TheRealKasumi/NikoLight/mcu/src/led/driver/Pixel.cpp

/**
 * @file Pixel.cpp
 * @author TheRealKasumi
 * @brief Implementation of the {@link NL::Pixel} class.
 *
 * @copyright Copyright (c) 2023 TheRealKasumi
 *
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
 */
#include "led/driver/Pixel.h"

/**
 * @brief Create a new instance of {@link NL::Pixel}.
 */
NL::Pixel::Pixel()
{
	this->setColor(NL::Pixel::ColorCode::Black);
}

/**
 * @brief Create a new instance of {@link NL::Pixel}.
 * @param colorCode 24 bit color code
 */
NL::Pixel::Pixel(const uint32_t colorCode)
{
	this->setColor(colorCode);
}

/**
 * @brief Create a new instance of {@link NL::Pixel}.
 * @param colorCode one of the html color codes
 */
NL::Pixel::Pixel(const NL::Pixel::ColorCode colorCode)
{
	this->setColor(colorCode);
}

/**
 * @brief Create a new instance of {@link NL::Pixel}.
 * @param red red value
 * @param green green value
 * @param blue blue value
 */
NL::Pixel::Pixel(const uint8_t red, const uint8_t green, const uint8_t blue)
{
	this->setColor(red, green, blue);
}

/***
 * Destroy the {@link NL::Pixel} isntance.
 */
NL::Pixel::~Pixel()
{
}

/**
 * @brief Set the pixel color.
 * @param colorCode 24 bit color code
 */
void NL::Pixel::setColor(const uint32_t colorCode)
{
	this->red = (colorCode & 0xff0000) >> 16;
	this->green = (colorCode & 0x00ff00) >> 8;
	this->blue = (colorCode & 0x0000ff);
}

/**
 * @brief Set the pixel color.
 * @param colorCode one of the html color codes
 */
void NL::Pixel::setColor(const NL::Pixel::ColorCode colorCode)
{
	this->red = (static_cast<uint32_t>(colorCode) & 0xff0000) >> 16;
	this->green = (static_cast<uint32_t>(colorCode) & 0x00ff00) >> 8;
	this->blue = (static_cast<uint32_t>(colorCode) & 0x0000ff);
}

/**
 * @brief Set the pixel color.
 * @param red red value
 * @param green green value
 * @param blue blue value
 */
void NL::Pixel::setColor(const uint8_t red, const uint8_t green, const uint8_t blue)
{
	this->red = red;
	this->green = green;
	this->blue = blue;
}
