TheRealKasumi/NikoLight/mcu/src/server/ResetEndpoint.cpp

/**
 * @file ResetEndpoint.h
 * @author TheRealKasumi
 * @brief Contains a REST endpoint to remotely reset the controller in case something is going wrong.
 *
 * @copyright Copyright (c) 2023 TheRealKasumi
 *
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
 */
#include "server/ResetEndpoint.h"

FS *NL::ResetEndpoint::fileSystem = nullptr;

/**
 * @brief Add all request handler for this {@link NL::RestEndpoint} to the {@link NL::WebServerManager}.
 */
void NL::ResetEndpoint::begin(FS *_fileSystem)
{
	NL::ResetEndpoint::fileSystem = _fileSystem;
	NL::WebServerManager::addRequestHandler((getBaseUri() + F("reset/soft")).c_str(), http_method::HTTP_POST, NL::ResetEndpoint::handleSoftReset);
	NL::WebServerManager::addRequestHandler((getBaseUri() + F("reset/hard")).c_str(), http_method::HTTP_POST, NL::ResetEndpoint::handleHardReset);
}

/**
 * @brief Handler function for the soft reset.
 */
void NL::ResetEndpoint::handleSoftReset()
{
	NL::Logger::log(NL::Logger::LogLevel::INFO, SOURCE_LOCATION, F("Received request to execute a soft reset."));
	NL::ResetEndpoint::sendSimpleResponse(200, F("I will reboot for you in 3 seconds."));
	NL::Updater::reboot(F("Soft Reset"), 3000);
}

/**
 * @brief Handler function for the hard reset. This also deletes the configuration to start with defaults.
 */
void NL::ResetEndpoint::handleHardReset()
{
	NL::Logger::log(NL::Logger::LogLevel::INFO, SOURCE_LOCATION, F("Received request to execute a hard reset."));
	NL::ResetEndpoint::sendSimpleResponse(200, F("I will reset my configuration and then reboot for you in 3 seconds."));

	if (!NL::ResetEndpoint::fileSystem->remove(CONFIGURATION_FILE_NAME))
	{
		NL::Logger::log(NL::Logger::LogLevel::WARN, SOURCE_LOCATION, F("Failed to remove configuration. This might be normal if it was not saved before."));
	}
	else
	{
		NL::Logger::log(NL::Logger::LogLevel::INFO, SOURCE_LOCATION, F("Configuration was reset."));
	}

	NL::Updater::reboot(F("Hard Reset"), 3000);
}
