TheRealKasumi/NikoLight/ui/pnpm-lock.yaml

lockfileVersion: '6.1'

settings:
  autoInstallPeers: true
  excludeLinksFromLockfile: false

dependencies:
  '@heroicons/react':
    specifier: ^2.0.16
    version: 2.0.16(react@18.2.0)
  '@radix-ui/react-alert-dialog':
    specifier: ^1.0.3
    version: 1.0.3(@types/react@18.0.28)(react-dom@18.2.0)(react@18.2.0)
  '@radix-ui/react-collapsible':
    specifier: ^1.0.2
    version: 1.0.2(react-dom@18.2.0)(react@18.2.0)
  '@radix-ui/react-select':
    specifier: ^1.2.1
    version: 1.2.1(@types/react@18.0.28)(react-dom@18.2.0)(react@18.2.0)
  '@radix-ui/react-slider':
    specifier: ^1.1.1
    version: 1.1.1(react-dom@18.2.0)(react@18.2.0)
  '@radix-ui/react-switch':
    specifier: ^1.0.2
    version: 1.0.2(react-dom@18.2.0)(react@18.2.0)
  '@radix-ui/react-toast':
    specifier: ^1.1.3
    version: 1.1.3(react-dom@18.2.0)(react@18.2.0)
  '@radix-ui/react-toggle-group':
    specifier: ^1.0.3
    version: 1.0.3(react-dom@18.2.0)(react@18.2.0)
  '@tanstack/react-query':
    specifier: ^4.27.0
    version: 4.27.0(react-dom@18.2.0)(react@18.2.0)
  '@tanstack/react-router':
    specifier: 0.0.1-beta.83
    version: 0.0.1-beta.83(react-dom@18.2.0)(react@18.2.0)
  file-saver:
    specifier: ^2.0.5
    version: 2.0.5
  hex-rgb:
    specifier: ^5.0.0
    version: 5.0.0
  i18next:
    specifier: ^22.4.12
    version: 22.4.12
  i18next-browser-languagedetector:
    specifier: ^7.0.1
    version: 7.0.1
  i18next-http-backend:
    specifier: ^2.2.0
    version: 2.2.0
  ky:
    specifier: ^0.33.3
    version: 0.33.3
  react:
    specifier: ^18.2.0
    version: 18.2.0
  react-dom:
    specifier: ^18.2.0
    version: 18.2.0(react@18.2.0)
  react-error-boundary:
    specifier: ^3.1.4
    version: 3.1.4(react@18.2.0)
  react-hook-form:
    specifier: ^7.43.7
    version: 7.43.7(react@18.2.0)
  react-i18next:
    specifier: ^12.2.0
    version: 12.2.0(i18next@22.4.12)(react-dom@18.2.0)(react@18.2.0)
  rgb-hex:
    specifier: ^4.0.1
    version: 4.0.1
  swagger-ui-react:
    specifier: ^4.18.1
    version: 4.18.1(@types/react-dom@18.0.11)(@types/react@18.0.28)(react-dom@18.2.0)(react@18.2.0)

devDependencies:
  '@tanstack/eslint-plugin-query':
    specifier: ^4.27.0
    version: 4.27.0
  '@tanstack/react-query-devtools':
    specifier: ^4.27.0
    version: 4.27.0(@tanstack/react-query@4.27.0)(react-dom@18.2.0)(react@18.2.0)
  '@tanstack/react-router-devtools':
    specifier: 0.0.1-beta.83
    version: 0.0.1-beta.83(react-dom@18.2.0)(react@18.2.0)
  '@types/file-saver':
    specifier: ^2.0.5
    version: 2.0.5
  '@types/prettier':
    specifier: ^2.7.2
    version: 2.7.2
  '@types/react':
    specifier: ^18.0.28
    version: 18.0.28
  '@types/react-dom':
    specifier: ^18.0.11
    version: 18.0.11
  '@types/swagger-ui-react':
    specifier: ^4.11.0
    version: 4.11.0
  '@typescript-eslint/eslint-plugin':
    specifier: ^5.55.0
    version: 5.55.0(@typescript-eslint/parser@5.55.0)(eslint@8.36.0)(typescript@5.0.2)
  '@typescript-eslint/parser':
    specifier: ^5.55.0
    version: 5.55.0(eslint@8.36.0)(typescript@5.0.2)
  '@vitejs/plugin-react':
    specifier: ^3.1.0
    version: 3.1.0(vite@4.2.0)
  autoprefixer:
    specifier: ^10.4.14
    version: 10.4.14(postcss@8.4.21)
  classnames:
    specifier: ^2.3.2
    version: 2.3.2
  cssnano:
    specifier: ^5.1.15
    version: 5.1.15(postcss@8.4.21)
  eslint:
    specifier: ^8.36.0
    version: 8.36.0
  eslint-config-prettier:
    specifier: ^8.7.0
    version: 8.7.0(eslint@8.36.0)
  eslint-plugin-prettier:
    specifier: ^4.2.1
    version: 4.2.1(eslint-config-prettier@8.7.0)(eslint@8.36.0)(prettier@2.8.4)
  eslint-plugin-react:
    specifier: ^7.32.2
    version: 7.32.2(eslint@8.36.0)
  eslint-plugin-react-hooks:
    specifier: ^4.6.0
    version: 4.6.0(eslint@8.36.0)
  msw:
    specifier: ^1.1.0
    version: 1.1.0(typescript@5.0.2)
  postcss:
    specifier: ^8.4.21
    version: 8.4.21
  prettier:
    specifier: ^2.8.4
    version: 2.8.4
  prettier-plugin-tailwindcss:
    specifier: ^0.2.5
    version: 0.2.5(prettier@2.8.4)
  tailwind-merge:
    specifier: ^1.10.0
    version: 1.10.0
  tailwindcss:
    specifier: ^3.2.7
    version: 3.2.7(postcss@8.4.21)
  tailwindcss-radix:
    specifier: ^2.8.0
    version: 2.8.0
  typescript:
    specifier: ^5.0.2
    version: 5.0.2
  vite:
    specifier: ^4.2.0
    version: 4.2.0
  vite-plugin-svgr:
    specifier: ^2.4.0
    version: 2.4.0(vite@4.2.0)

packages:

  /@ampproject/remapping@2.2.0:
    resolution: {integrity: sha512-qRmjj8nj9qmLTQXXmaR1cck3UXSRMPrbsLJAasZpF+t3riI71BXed5ebIOYwQntykeZuhjsdweEc9BxH5Jc26w==}
    engines: {node: '>=6.0.0'}
    dependencies:
      '@jridgewell/gen-mapping': 0.1.1
      '@jridgewell/trace-mapping': 0.3.17
    dev: true

  /@babel/code-frame@7.18.6:
    resolution: {integrity: sha512-TDCmlK5eOvH+eH7cdAFlNXeVJqWIQ7gW9tY1GJIpUtFb6CmjVyq2VM3u71bOyR8CRihcCgMUYoDNyLXao3+70Q==}
    engines: {node: '>=6.9.0'}
    dependencies:
      '@babel/highlight': 7.18.6
    dev: true

  /@babel/compat-data@7.20.0:
    resolution: {integrity: sha512-Gt9jszFJYq7qzXVK4slhc6NzJXnOVmRECWcVjF/T23rNXD9NtWQ0W3qxdg+p9wWIB+VQw3GYV/U2Ha9bRTfs4w==}
    engines: {node: '>=6.9.0'}
    dev: true

  /@babel/compat-data@7.20.10:
    resolution: {integrity: sha512-sEnuDPpOJR/fcafHMjpcpGN5M2jbUGUHwmuWKM/YdPzeEDJg8bgmbcWQFUfE32MQjti1koACvoPVsDe8Uq+idg==}
    engines: {node: '>=6.9.0'}
    dev: true

  /@babel/core@7.20.12:
    resolution: {integrity: sha512-XsMfHovsUYHFMdrIHkZphTN/2Hzzi78R08NuHfDBehym2VsPDL6Zn/JAD/JQdnRvbSsbQc4mVaU1m6JgtTEElg==}
    engines: {node: '>=6.9.0'}
    dependencies:
      '@ampproject/remapping': 2.2.0
      '@babel/code-frame': 7.18.6
      '@babel/generator': 7.20.7
      '@babel/helper-compilation-targets': 7.20.7(@babel/core@7.20.12)
      '@babel/helper-module-transforms': 7.20.11
      '@babel/helpers': 7.20.7
      '@babel/parser': 7.20.7
      '@babel/template': 7.20.7
      '@babel/traverse': 7.20.12
      '@babel/types': 7.20.7
      convert-source-map: 1.9.0
      debug: 4.3.4
      gensync: 1.0.0-beta.2
      json5: 2.2.3
      semver: 6.3.0
    transitivePeerDependencies:
      - supports-color
    dev: true

  /@babel/core@7.20.5:
    resolution: {integrity: sha512-UdOWmk4pNWTm/4DlPUl/Pt4Gz4rcEMb7CY0Y3eJl5Yz1vI8ZJGmHWaVE55LoxRjdpx0z259GE9U5STA9atUinQ==}
    engines: {node: '>=6.9.0'}
    dependencies:
      '@ampproject/remapping': 2.2.0
      '@babel/code-frame': 7.18.6
      '@babel/generator': 7.20.5
      '@babel/helper-compilation-targets': 7.20.0(@babel/core@7.20.5)
      '@babel/helper-module-transforms': 7.20.2
      '@babel/helpers': 7.20.6
      '@babel/parser': 7.20.5
      '@babel/template': 7.18.10
      '@babel/traverse': 7.20.5
      '@babel/types': 7.20.5
      convert-source-map: 1.9.0
      debug: 4.3.4
      gensync: 1.0.0-beta.2
      json5: 2.2.1
      semver: 6.3.0
    transitivePeerDependencies:
      - supports-color
    dev: true

  /@babel/generator@7.20.5:
    resolution: {integrity: sha512-jl7JY2Ykn9S0yj4DQP82sYvPU+T3g0HFcWTqDLqiuA9tGRNIj9VfbtXGAYTTkyNEnQk1jkMGOdYka8aG/lulCA==}
    engines: {node: '>=6.9.0'}
    dependencies:
      '@babel/types': 7.20.5
      '@jridgewell/gen-mapping': 0.3.2
      jsesc: 2.5.2
    dev: true

  /@babel/generator@7.20.7:
    resolution: {integrity: sha512-7wqMOJq8doJMZmP4ApXTzLxSr7+oO2jroJURrVEp6XShrQUObV8Tq/D0NCcoYg2uHqUrjzO0zwBjoYzelxK+sw==}
    engines: {node: '>=6.9.0'}
    dependencies:
      '@babel/types': 7.20.7
      '@jridgewell/gen-mapping': 0.3.2
      jsesc: 2.5.2
    dev: true

  /@babel/helper-compilation-targets@7.20.0(@babel/core@7.20.5):
    resolution: {integrity: sha512-0jp//vDGp9e8hZzBc6N/KwA5ZK3Wsm/pfm4CrY7vzegkVxc65SgSn6wYOnwHe9Js9HRQ1YTCKLGPzDtaS3RoLQ==}
    engines: {node: '>=6.9.0'}
    peerDependencies:
      '@babel/core': ^7.0.0
    dependencies:
      '@babel/compat-data': 7.20.0
      '@babel/core': 7.20.5
      '@babel/helper-validator-option': 7.18.6
      browserslist: 4.21.5
      semver: 6.3.0
    dev: true

  /@babel/helper-compilation-targets@7.20.7(@babel/core@7.20.12):
    resolution: {integrity: sha512-4tGORmfQcrc+bvrjb5y3dG9Mx1IOZjsHqQVUz7XCNHO+iTmqxWnVg3KRygjGmpRLJGdQSKuvFinbIb0CnZwHAQ==}
    engines: {node: '>=6.9.0'}
    peerDependencies:
      '@babel/core': ^7.0.0
    dependencies:
      '@babel/compat-data': 7.20.10
      '@babel/core': 7.20.12
      '@babel/helper-validator-option': 7.18.6
      browserslist: 4.21.5
      lru-cache: 5.1.1
      semver: 6.3.0
    dev: true

  /@babel/helper-environment-visitor@7.18.9:
    resolution: {integrity: sha512-3r/aACDJ3fhQ/EVgFy0hpj8oHyHpQc+LPtJoY9SzTThAsStm4Ptegq92vqKoE3vD706ZVFWITnMnxucw+S9Ipg==}
    engines: {node: '>=6.9.0'}
    dev: true

  /@babel/helper-function-name@7.19.0:
    resolution: {integrity: sha512-WAwHBINyrpqywkUH0nTnNgI5ina5TFn85HKS0pbPDfxFfhyR/aNQEn4hGi1P1JyT//I0t4OgXUlofzWILRvS5w==}
    engines: {node: '>=6.9.0'}
    dependencies:
      '@babel/template': 7.18.10
      '@babel/types': 7.20.5
    dev: true

  /@babel/helper-hoist-variables@7.18.6:
    resolution: {integrity: sha512-UlJQPkFqFULIcyW5sbzgbkxn2FKRgwWiRexcuaR8RNJRy8+LLveqPjwZV/bwrLZCN0eUHD/x8D0heK1ozuoo6Q==}
    engines: {node: '>=6.9.0'}
    dependencies:
      '@babel/types': 7.20.5
    dev: true

  /@babel/helper-module-imports@7.18.6:
    resolution: {integrity: sha512-0NFvs3VkuSYbFi1x2Vd6tKrywq+z/cLeYC/RJNFrIX/30Bf5aiGYbtvGXolEktzJH8o5E5KJ3tT+nkxuuZFVlA==}
    engines: {node: '>=6.9.0'}
    dependencies:
      '@babel/types': 7.20.5
    dev: true

  /@babel/helper-module-transforms@7.20.11:
    resolution: {integrity: sha512-uRy78kN4psmji1s2QtbtcCSaj/LILFDp0f/ymhpQH5QY3nljUZCaNWz9X1dEj/8MBdBEFECs7yRhKn8i7NjZgg==}
    engines: {node: '>=6.9.0'}
    dependencies:
      '@babel/helper-environment-visitor': 7.18.9
      '@babel/helper-module-imports': 7.18.6
      '@babel/helper-simple-access': 7.20.2
      '@babel/helper-split-export-declaration': 7.18.6
      '@babel/helper-validator-identifier': 7.19.1
      '@babel/template': 7.20.7
      '@babel/traverse': 7.20.12
      '@babel/types': 7.20.7
    transitivePeerDependencies:
      - supports-color
    dev: true

  /@babel/helper-module-transforms@7.20.2:
    resolution: {integrity: sha512-zvBKyJXRbmK07XhMuujYoJ48B5yvvmM6+wcpv6Ivj4Yg6qO7NOZOSnvZN9CRl1zz1Z4cKf8YejmCMh8clOoOeA==}
    engines: {node: '>=6.9.0'}
    dependencies:
      '@babel/helper-environment-visitor': 7.18.9
      '@babel/helper-module-imports': 7.18.6
      '@babel/helper-simple-access': 7.20.2
      '@babel/helper-split-export-declaration': 7.18.6
      '@babel/helper-validator-identifier': 7.19.1
      '@babel/template': 7.18.10
      '@babel/traverse': 7.20.5
      '@babel/types': 7.20.5
    transitivePeerDependencies:
      - supports-color
    dev: true

  /@babel/helper-plugin-utils@7.19.0:
    resolution: {integrity: sha512-40Ryx7I8mT+0gaNxm8JGTZFUITNqdLAgdg0hXzeVZxVD6nFsdhQvip6v8dqkRHzsz1VFpFAaOCHNn0vKBL7Czw==}
    engines: {node: '>=6.9.0'}
    dev: true

  /@babel/helper-simple-access@7.20.2:
    resolution: {integrity: sha512-+0woI/WPq59IrqDYbVGfshjT5Dmk/nnbdpcF8SnMhhXObpTq2KNBdLFRFrkVdbDOyUmHBCxzm5FHV1rACIkIbA==}
    engines: {node: '>=6.9.0'}
    dependencies:
      '@babel/types': 7.20.5
    dev: true

  /@babel/helper-split-export-declaration@7.18.6:
    resolution: {integrity: sha512-bde1etTx6ZyTmobl9LLMMQsaizFVZrquTEHOqKeQESMKo4PlObf+8+JA25ZsIpZhT/WEd39+vOdLXAFG/nELpA==}
    engines: {node: '>=6.9.0'}
    dependencies:
      '@babel/types': 7.20.5
    dev: true

  /@babel/helper-string-parser@7.19.4:
    resolution: {integrity: sha512-nHtDoQcuqFmwYNYPz3Rah5ph2p8PFeFCsZk9A/48dPc/rGocJ5J3hAAZ7pb76VWX3fZKu+uEr/FhH5jLx7umrw==}
    engines: {node: '>=6.9.0'}
    dev: true

  /@babel/helper-validator-identifier@7.19.1:
    resolution: {integrity: sha512-awrNfaMtnHUr653GgGEs++LlAvW6w+DcPrOliSMXWCKo597CwL5Acf/wWdNkf/tfEQE3mjkeD1YOVZOUV/od1w==}
    engines: {node: '>=6.9.0'}
    dev: true

  /@babel/helper-validator-option@7.18.6:
    resolution: {integrity: sha512-XO7gESt5ouv/LRJdrVjkShckw6STTaB7l9BrpBaAHDeF5YZT+01PCwmR0SJHnkW6i8OwW/EVWRShfi4j2x+KQw==}
    engines: {node: '>=6.9.0'}
    dev: true

  /@babel/helpers@7.20.6:
    resolution: {integrity: sha512-Pf/OjgfgFRW5bApskEz5pvidpim7tEDPlFtKcNRXWmfHGn9IEI2W2flqRQXTFb7gIPTyK++N6rVHuwKut4XK6w==}
    engines: {node: '>=6.9.0'}
    dependencies:
      '@babel/template': 7.18.10
      '@babel/traverse': 7.20.5
      '@babel/types': 7.20.5
    transitivePeerDependencies:
      - supports-color
    dev: true

  /@babel/helpers@7.20.7:
    resolution: {integrity: sha512-PBPjs5BppzsGaxHQCDKnZ6Gd9s6xl8bBCluz3vEInLGRJmnZan4F6BYCeqtyXqkk4W5IlPmjK4JlOuZkpJ3xZA==}
    engines: {node: '>=6.9.0'}
    dependencies:
      '@babel/template': 7.20.7
      '@babel/traverse': 7.20.12
      '@babel/types': 7.20.7
    transitivePeerDependencies:
      - supports-color
    dev: true

  /@babel/highlight@7.18.6:
    resolution: {integrity: sha512-u7stbOuYjaPezCuLj29hNW1v64M2Md2qupEKP1fHc7WdOA3DgLh37suiSrZYY7haUB7iBeQZ9P1uiRF359do3g==}
    engines: {node: '>=6.9.0'}
    dependencies:
      '@babel/helper-validator-identifier': 7.19.1
      chalk: 2.4.2
      js-tokens: 4.0.0
    dev: true

  /@babel/parser@7.20.5:
    resolution: {integrity: sha512-r27t/cy/m9uKLXQNWWebeCUHgnAZq0CpG1OwKRxzJMP1vpSU4bSIK2hq+/cp0bQxetkXx38n09rNu8jVkcK/zA==}
    engines: {node: '>=6.0.0'}
    hasBin: true
    dependencies:
      '@babel/types': 7.20.5
    dev: true

  /@babel/parser@7.20.7:
    resolution: {integrity: sha512-T3Z9oHybU+0vZlY9CiDSJQTD5ZapcW18ZctFMi0MOAl/4BjFF4ul7NVSARLdbGO5vDqy9eQiGTV0LtKfvCYvcg==}
    engines: {node: '>=6.0.0'}
    hasBin: true
    dependencies:
      '@babel/types': 7.20.7
    dev: true

  /@babel/plugin-transform-react-jsx-self@7.18.6(@babel/core@7.20.12):
    resolution: {integrity: sha512-A0LQGx4+4Jv7u/tWzoJF7alZwnBDQd6cGLh9P+Ttk4dpiL+J5p7NSNv/9tlEFFJDq3kjxOavWmbm6t0Gk+A3Ig==}
    engines: {node: '>=6.9.0'}
    peerDependencies:
      '@babel/core': ^7.0.0-0
    dependencies:
      '@babel/core': 7.20.12
      '@babel/helper-plugin-utils': 7.19.0
    dev: true

  /@babel/plugin-transform-react-jsx-source@7.19.6(@babel/core@7.20.12):
    resolution: {integrity: sha512-RpAi004QyMNisst/pvSanoRdJ4q+jMCWyk9zdw/CyLB9j8RXEahodR6l2GyttDRyEVWZtbN+TpLiHJ3t34LbsQ==}
    engines: {node: '>=6.9.0'}
    peerDependencies:
      '@babel/core': ^7.0.0-0
    dependencies:
      '@babel/core': 7.20.12
      '@babel/helper-plugin-utils': 7.19.0
    dev: true

  /@babel/runtime-corejs3@7.21.0:
    resolution: {integrity: sha512-TDD4UJzos3JJtM+tHX+w2Uc+KWj7GV+VKKFdMVd2Rx8sdA19hcc3P3AHFYd5LVOw+pYuSd5lICC3gm52B6Rwxw==}
    engines: {node: '>=6.9.0'}
    dependencies:
      core-js-pure: 3.26.1
      regenerator-runtime: 0.13.11
    dev: false

  /@babel/runtime@7.20.1:
    resolution: {integrity: sha512-mrzLkl6U9YLF8qpqI7TB82PESyEGjm/0Ly91jG575eVxMMlb8fYfOXFZIJ8XfLrJZQbm7dlKry2bJmXBUEkdFg==}
    engines: {node: '>=6.9.0'}
    dependencies:
      regenerator-runtime: 0.13.11
    dev: false

  /@babel/runtime@7.20.7:
    resolution: {integrity: sha512-UF0tvkUtxwAgZ5W/KrkHf0Rn0fdnLDU9ScxBrEVNUprE/MzirjK4MJUX1/BVDv00Sv8cljtukVK1aky++X1SjQ==}
    engines: {node: '>=6.9.0'}
    dependencies:
      regenerator-runtime: 0.13.11

  /@babel/template@7.18.10:
    resolution: {integrity: sha512-TI+rCtooWHr3QJ27kJxfjutghu44DLnasDMwpDqCXVTal9RLp3RSYNh4NdBrRP2cQAoG9A8juOQl6P6oZG4JxA==}
    engines: {node: '>=6.9.0'}
    dependencies:
      '@babel/code-frame': 7.18.6
      '@babel/parser': 7.20.5
      '@babel/types': 7.20.5
    dev: true

  /@babel/template@7.20.7:
    resolution: {integrity: sha512-8SegXApWe6VoNw0r9JHpSteLKTpTiLZ4rMlGIm9JQ18KiCtyQiAMEazujAHrUS5flrcqYZa75ukev3P6QmUwUw==}
    engines: {node: '>=6.9.0'}
    dependencies:
      '@babel/code-frame': 7.18.6
      '@babel/parser': 7.20.7
      '@babel/types': 7.20.7
    dev: true

  /@babel/traverse@7.20.12:
    resolution: {integrity: sha512-MsIbFN0u+raeja38qboyF8TIT7K0BFzz/Yd/77ta4MsUsmP2RAnidIlwq7d5HFQrH/OZJecGV6B71C4zAgpoSQ==}
    engines: {node: '>=6.9.0'}
    dependencies:
      '@babel/code-frame': 7.18.6
      '@babel/generator': 7.20.7
      '@babel/helper-environment-visitor': 7.18.9
      '@babel/helper-function-name': 7.19.0
      '@babel/helper-hoist-variables': 7.18.6
      '@babel/helper-split-export-declaration': 7.18.6
      '@babel/parser': 7.20.7
      '@babel/types': 7.20.7
      debug: 4.3.4
      globals: 11.12.0
    transitivePeerDependencies:
      - supports-color
    dev: true

  /@babel/traverse@7.20.5:
    resolution: {integrity: sha512-WM5ZNN3JITQIq9tFZaw1ojLU3WgWdtkxnhM1AegMS+PvHjkM5IXjmYEGY7yukz5XS4sJyEf2VzWjI8uAavhxBQ==}
    engines: {node: '>=6.9.0'}
    dependencies:
      '@babel/code-frame': 7.18.6
      '@babel/generator': 7.20.5
      '@babel/helper-environment-visitor': 7.18.9
      '@babel/helper-function-name': 7.19.0
      '@babel/helper-hoist-variables': 7.18.6
      '@babel/helper-split-export-declaration': 7.18.6
      '@babel/parser': 7.20.5
      '@babel/types': 7.20.5
      debug: 4.3.4
      globals: 11.12.0
    transitivePeerDependencies:
      - supports-color
    dev: true

  /@babel/types@7.20.5:
    resolution: {integrity: sha512-c9fst/h2/dcF7H+MJKZ2T0KjEQ8hY/BNnDk/H3XY8C4Aw/eWQXWn/lWntHF9ooUBnGmEvbfGrTgLWc+um0YDUg==}
    engines: {node: '>=6.9.0'}
    dependencies:
      '@babel/helper-string-parser': 7.19.4
      '@babel/helper-validator-identifier': 7.19.1
      to-fast-properties: 2.0.0
    dev: true

  /@babel/types@7.20.7:
    resolution: {integrity: sha512-69OnhBxSSgK0OzTJai4kyPDiKTIe3j+ctaHdIGVbRahTLAT7L3R9oeXHC2aVSuGYt3cVnoAMDmOCgJ2yaiLMvg==}
    engines: {node: '>=6.9.0'}
    dependencies:
      '@babel/helper-string-parser': 7.19.4
      '@babel/helper-validator-identifier': 7.19.1
      to-fast-properties: 2.0.0
    dev: true

  /@braintree/sanitize-url@6.0.2:
    resolution: {integrity: sha512-Tbsj02wXCbqGmzdnXNk0SOF19ChhRU70BsroIi4Pm6Ehp56in6vch94mfbdQ17DozxkL3BAVjbZ4Qc1a0HFRAg==}
    dev: false

  /@esbuild/android-arm64@0.17.12:
    resolution: {integrity: sha512-WQ9p5oiXXYJ33F2EkE3r0FRDFVpEdcDiwNX3u7Xaibxfx6vQE0Sb8ytrfQsA5WO6kDn6mDfKLh6KrPBjvkk7xA==}
    engines: {node: '>=12'}
    cpu: [arm64]
    os: [android]
    requiresBuild: true
    dev: true
    optional: true

  /@esbuild/android-arm@0.17.12:
    resolution: {integrity: sha512-E/sgkvwoIfj4aMAPL2e35VnUJspzVYl7+M1B2cqeubdBhADV4uPon0KCc8p2G+LqSJ6i8ocYPCqY3A4GGq0zkQ==}
    engines: {node: '>=12'}
    cpu: [arm]
    os: [android]
    requiresBuild: true
    dev: true
    optional: true

  /@esbuild/android-x64@0.17.12:
    resolution: {integrity: sha512-m4OsaCr5gT+se25rFPHKQXARMyAehHTQAz4XX1Vk3d27VtqiX0ALMBPoXZsGaB6JYryCLfgGwUslMqTfqeLU0w==}
    engines: {node: '>=12'}
    cpu: [x64]
    os: [android]
    requiresBuild: true
    dev: true
    optional: true

  /@esbuild/darwin-arm64@0.17.12:
    resolution: {integrity: sha512-O3GCZghRIx+RAN0NDPhyyhRgwa19MoKlzGonIb5hgTj78krqp9XZbYCvFr9N1eUxg0ZQEpiiZ4QvsOQwBpP+lg==}
    engines: {node: '>=12'}
    cpu: [arm64]
    os: [darwin]
    requiresBuild: true
    dev: true
    optional: true

  /@esbuild/darwin-x64@0.17.12:
    resolution: {integrity: sha512-5D48jM3tW27h1qjaD9UNRuN+4v0zvksqZSPZqeSWggfMlsVdAhH3pwSfQIFJwcs9QJ9BRibPS4ViZgs3d2wsCA==}
    engines: {node: '>=12'}
    cpu: [x64]
    os: [darwin]
    requiresBuild: true
    dev: true
    optional: true

  /@esbuild/freebsd-arm64@0.17.12:
    resolution: {integrity: sha512-OWvHzmLNTdF1erSvrfoEBGlN94IE6vCEaGEkEH29uo/VoONqPnoDFfShi41Ew+yKimx4vrmmAJEGNoyyP+OgOQ==}
    engines: {node: '>=12'}
    cpu: [arm64]
    os: [freebsd]
    requiresBuild: true
    dev: true
    optional: true

  /@esbuild/freebsd-x64@0.17.12:
    resolution: {integrity: sha512-A0Xg5CZv8MU9xh4a+7NUpi5VHBKh1RaGJKqjxe4KG87X+mTjDE6ZvlJqpWoeJxgfXHT7IMP9tDFu7IZ03OtJAw==}
    engines: {node: '>=12'}
    cpu: [x64]
    os: [freebsd]
    requiresBuild: true
    dev: true
    optional: true

  /@esbuild/linux-arm64@0.17.12:
    resolution: {integrity: sha512-cK3AjkEc+8v8YG02hYLQIQlOznW+v9N+OI9BAFuyqkfQFR+DnDLhEM5N8QRxAUz99cJTo1rLNXqRrvY15gbQUg==}
    engines: {node: '>=12'}
    cpu: [arm64]
    os: [linux]
    requiresBuild: true
    dev: true
    optional: true

  /@esbuild/linux-arm@0.17.12:
    resolution: {integrity: sha512-WsHyJ7b7vzHdJ1fv67Yf++2dz3D726oO3QCu8iNYik4fb5YuuReOI9OtA+n7Mk0xyQivNTPbl181s+5oZ38gyA==}
    engines: {node: '>=12'}
    cpu: [arm]
    os: [linux]
    requiresBuild: true
    dev: true
    optional: true

  /@esbuild/linux-ia32@0.17.12:
    resolution: {integrity: sha512-jdOBXJqcgHlah/nYHnj3Hrnl9l63RjtQ4vn9+bohjQPI2QafASB5MtHAoEv0JQHVb/xYQTFOeuHnNYE1zF7tYw==}
    engines: {node: '>=12'}
    cpu: [ia32]
    os: [linux]
    requiresBuild: true
    dev: true
    optional: true

  /@esbuild/linux-loong64@0.17.12:
    resolution: {integrity: sha512-GTOEtj8h9qPKXCyiBBnHconSCV9LwFyx/gv3Phw0pa25qPYjVuuGZ4Dk14bGCfGX3qKF0+ceeQvwmtI+aYBbVA==}
    engines: {node: '>=12'}
    cpu: [loong64]
    os: [linux]
    requiresBuild: true
    dev: true
    optional: true

  /@esbuild/linux-mips64el@0.17.12:
    resolution: {integrity: sha512-o8CIhfBwKcxmEENOH9RwmUejs5jFiNoDw7YgS0EJTF6kgPgcqLFjgoc5kDey5cMHRVCIWc6kK2ShUePOcc7RbA==}
    engines: {node: '>=12'}
    cpu: [mips64el]
    os: [linux]
    requiresBuild: true
    dev: true
    optional: true

  /@esbuild/linux-ppc64@0.17.12:
    resolution: {integrity: sha512-biMLH6NR/GR4z+ap0oJYb877LdBpGac8KfZoEnDiBKd7MD/xt8eaw1SFfYRUeMVx519kVkAOL2GExdFmYnZx3A==}
    engines: {node: '>=12'}
    cpu: [ppc64]
    os: [linux]
    requiresBuild: true
    dev: true
    optional: true

  /@esbuild/linux-riscv64@0.17.12:
    resolution: {integrity: sha512-jkphYUiO38wZGeWlfIBMB72auOllNA2sLfiZPGDtOBb1ELN8lmqBrlMiucgL8awBw1zBXN69PmZM6g4yTX84TA==}
    engines: {node: '>=12'}
    cpu: [riscv64]
    os: [linux]
    requiresBuild: true
    dev: true
    optional: true

  /@esbuild/linux-s390x@0.17.12:
    resolution: {integrity: sha512-j3ucLdeY9HBcvODhCY4b+Ds3hWGO8t+SAidtmWu/ukfLLG/oYDMaA+dnugTVAg5fnUOGNbIYL9TOjhWgQB8W5g==}
    engines: {node: '>=12'}
    cpu: [s390x]
    os: [linux]
    requiresBuild: true
    dev: true
    optional: true

  /@esbuild/linux-x64@0.17.12:
    resolution: {integrity: sha512-uo5JL3cgaEGotaqSaJdRfFNSCUJOIliKLnDGWaVCgIKkHxwhYMm95pfMbWZ9l7GeW9kDg0tSxcy9NYdEtjwwmA==}
    engines: {node: '>=12'}
    cpu: [x64]
    os: [linux]
    requiresBuild: true
    dev: true
    optional: true

  /@esbuild/netbsd-x64@0.17.12:
    resolution: {integrity: sha512-DNdoRg8JX+gGsbqt2gPgkgb00mqOgOO27KnrWZtdABl6yWTST30aibGJ6geBq3WM2TIeW6COs5AScnC7GwtGPg==}
    engines: {node: '>=12'}
    cpu: [x64]
    os: [netbsd]
    requiresBuild: true
    dev: true
    optional: true

  /@esbuild/openbsd-x64@0.17.12:
    resolution: {integrity: sha512-aVsENlr7B64w8I1lhHShND5o8cW6sB9n9MUtLumFlPhG3elhNWtE7M1TFpj3m7lT3sKQUMkGFjTQBrvDDO1YWA==}
    engines: {node: '>=12'}
    cpu: [x64]
    os: [openbsd]
    requiresBuild: true
    dev: true
    optional: true

  /@esbuild/sunos-x64@0.17.12:
    resolution: {integrity: sha512-qbHGVQdKSwi0JQJuZznS4SyY27tYXYF0mrgthbxXrZI3AHKuRvU+Eqbg/F0rmLDpW/jkIZBlCO1XfHUBMNJ1pg==}
    engines: {node: '>=12'}
    cpu: [x64]
    os: [sunos]
    requiresBuild: true
    dev: true
    optional: true

  /@esbuild/win32-arm64@0.17.12:
    resolution: {integrity: sha512-zsCp8Ql+96xXTVTmm6ffvoTSZSV2B/LzzkUXAY33F/76EajNw1m+jZ9zPfNJlJ3Rh4EzOszNDHsmG/fZOhtqDg==}
    engines: {node: '>=12'}
    cpu: [arm64]
    os: [win32]
    requiresBuild: true
    dev: true
    optional: true

  /@esbuild/win32-ia32@0.17.12:
    resolution: {integrity: sha512-FfrFjR4id7wcFYOdqbDfDET3tjxCozUgbqdkOABsSFzoZGFC92UK7mg4JKRc/B3NNEf1s2WHxJ7VfTdVDPN3ng==}
    engines: {node: '>=12'}
    cpu: [ia32]
    os: [win32]
    requiresBuild: true
    dev: true
    optional: true

  /@esbuild/win32-x64@0.17.12:
    resolution: {integrity: sha512-JOOxw49BVZx2/5tW3FqkdjSD/5gXYeVGPDcB0lvap0gLQshkh1Nyel1QazC+wNxus3xPlsYAgqU1BUmrmCvWtw==}
    engines: {node: '>=12'}
    cpu: [x64]
    os: [win32]
    requiresBuild: true
    dev: true
    optional: true

  /@eslint-community/eslint-utils@4.3.0(eslint@8.36.0):
    resolution: {integrity: sha512-v3oplH6FYCULtFuCeqyuTd9D2WKO937Dxdq+GmHOLL72TTRriLxz2VLlNfkZRsvj6PKnOPAtuT6dwrs/pA5DvA==}
    engines: {node: ^12.22.0 || ^14.17.0 || >=16.0.0}
    peerDependencies:
      eslint: ^6.0.0 || ^7.0.0 || >=8.0.0
    dependencies:
      eslint: 8.36.0
      eslint-visitor-keys: 3.3.0
    dev: true

  /@eslint-community/regexpp@4.4.0:
    resolution: {integrity: sha512-A9983Q0LnDGdLPjxyXQ00sbV+K+O+ko2Dr+CZigbHWtX9pNfxlaBkMR8X1CztI73zuEyEBXTVjx7CE+/VSwDiQ==}
    engines: {node: ^12.0.0 || ^14.0.0 || >=16.0.0}
    dev: true

  /@eslint/eslintrc@2.0.1:
    resolution: {integrity: sha512-eFRmABvW2E5Ho6f5fHLqgena46rOj7r7OKHYfLElqcBfGFHHpjBhivyi5+jOEQuSpdc/1phIZJlbC2te+tZNIw==}
    engines: {node: ^12.22.0 || ^14.17.0 || >=16.0.0}
    dependencies:
      ajv: 6.12.6
      debug: 4.3.4
      espree: 9.5.0
      globals: 13.19.0
      ignore: 5.2.1
      import-fresh: 3.3.0
      js-yaml: 4.1.0
      minimatch: 3.1.2
      strip-json-comments: 3.1.1
    transitivePeerDependencies:
      - supports-color
    dev: true

  /@eslint/js@8.36.0:
    resolution: {integrity: sha512-lxJ9R5ygVm8ZWgYdUweoq5ownDlJ4upvoWmO4eLxBYHdMo+vZ/Rx0EN6MbKWDJOSUGrqJy2Gt+Dyv/VKml0fjg==}
    engines: {node: ^12.22.0 || ^14.17.0 || >=16.0.0}
    dev: true

  /@floating-ui/core@0.7.3:
    resolution: {integrity: sha512-buc8BXHmG9l82+OQXOFU3Kr2XQx9ys01U/Q9HMIrZ300iLc8HLMgh7dcCqgYzAzf4BkoQvDcXf5Y+CuEZ5JBYg==}
    dev: false

  /@floating-ui/dom@0.5.4:
    resolution: {integrity: sha512-419BMceRLq0RrmTSDxn8hf9R3VCJv2K9PUfugh5JyEFmdjzDo+e8U5EdR8nzKq8Yj1htzLm3b6eQEEam3/rrtg==}
    dependencies:
      '@floating-ui/core': 0.7.3
    dev: false

  /@floating-ui/react-dom@0.7.2(@types/react@18.0.28)(react-dom@18.2.0)(react@18.2.0):
    resolution: {integrity: sha512-1T0sJcpHgX/u4I1OzIEhlcrvkUN8ln39nz7fMoE/2HDHrPiMFoOGR7++GYyfUmIQHkkrTinaeQsO3XWubjSvGg==}
    peerDependencies:
      react: '>=16.8.0'
      react-dom: '>=16.8.0'
    dependencies:
      '@floating-ui/dom': 0.5.4
      react: 18.2.0
      react-dom: 18.2.0(react@18.2.0)
      use-isomorphic-layout-effect: 1.1.2(@types/react@18.0.28)(react@18.2.0)
    transitivePeerDependencies:
      - '@types/react'
    dev: false

  /@heroicons/react@2.0.16(react@18.2.0):
    resolution: {integrity: sha512-x89rFxH3SRdYaA+JCXwfe+RkE1SFTo9GcOkZettHer71Y3T7V+ogKmfw5CjTazgS3d0ClJ7p1NA+SP7VQLQcLw==}
    peerDependencies:
      react: '>= 16'
    dependencies:
      react: 18.2.0
    dev: false

  /@humanwhocodes/config-array@0.11.8:
    resolution: {integrity: sha512-UybHIJzJnR5Qc/MsD9Kr+RpO2h+/P1GhOwdiLPXK5TWk5sgTdu88bTD9UP+CKbPPh5Rni1u0GjAdYQLemG8g+g==}
    engines: {node: '>=10.10.0'}
    dependencies:
      '@humanwhocodes/object-schema': 1.2.1
      debug: 4.3.4
      minimatch: 3.1.2
    transitivePeerDependencies:
      - supports-color
    dev: true

  /@humanwhocodes/module-importer@1.0.1:
    resolution: {integrity: sha512-bxveV4V8v5Yb4ncFTT3rPSgZBOpCkjfK0y4oVVVJwIuDVBRMDXrPyXRL988i5ap9m9bnyEEjWfm5WkBmtffLfA==}
    engines: {node: '>=12.22'}
    dev: true

  /@humanwhocodes/object-schema@1.2.1:
    resolution: {integrity: sha512-ZnQMnLV4e7hDlUvw8H+U8ASL02SS2Gn6+9Ac3wGGLIe7+je2AeAOxPY+izIPJDfFDb7eDjev0Us8MO1iFRN8hA==}
    dev: true

  /@jridgewell/gen-mapping@0.1.1:
    resolution: {integrity: sha512-sQXCasFk+U8lWYEe66WxRDOE9PjVz4vSM51fTu3Hw+ClTpUSQb718772vH3pyS5pShp6lvQM7SxgIDXXXmOX7w==}
    engines: {node: '>=6.0.0'}
    dependencies:
      '@jridgewell/set-array': 1.1.2
      '@jridgewell/sourcemap-codec': 1.4.14
    dev: true

  /@jridgewell/gen-mapping@0.3.2:
    resolution: {integrity: sha512-mh65xKQAzI6iBcFzwv28KVWSmCkdRBWoOh+bYQGW3+6OZvbbN3TqMGo5hqYxQniRcH9F2VZIoJCm4pa3BPDK/A==}
    engines: {node: '>=6.0.0'}
    dependencies:
      '@jridgewell/set-array': 1.1.2
      '@jridgewell/sourcemap-codec': 1.4.14
      '@jridgewell/trace-mapping': 0.3.17
    dev: true

  /@jridgewell/resolve-uri@3.1.0:
    resolution: {integrity: sha512-F2msla3tad+Mfht5cJq7LSXcdudKTWCVYUgw6pLFOOHSTtZlj6SWNYAp+AhuqLmWdBO2X5hPrLcu8cVP8fy28w==}
    engines: {node: '>=6.0.0'}
    dev: true

  /@jridgewell/set-array@1.1.2:
    resolution: {integrity: sha512-xnkseuNADM0gt2bs+BvhO0p78Mk762YnZdsuzFV018NoG1Sj1SCQvpSqa7XUaTam5vAGasABV9qXASMKnFMwMw==}
    engines: {node: '>=6.0.0'}
    dev: true

  /@jridgewell/sourcemap-codec@1.4.14:
    resolution: {integrity: sha512-XPSJHWmi394fuUuzDnGz1wiKqWfo1yXecHQMRf2l6hztTO+nPru658AyDngaBe7isIxEkRsPR3FZh+s7iVa4Uw==}
    dev: true

  /@jridgewell/trace-mapping@0.3.17:
    resolution: {integrity: sha512-MCNzAp77qzKca9+W/+I0+sEpaUnZoeasnghNeVc41VZCEKaCH73Vq3BZZ/SzWIgrqE4H4ceI+p+b6C0mHf9T4g==}
    dependencies:
      '@jridgewell/resolve-uri': 3.1.0
      '@jridgewell/sourcemap-codec': 1.4.14
    dev: true

  /@mswjs/cookies@0.2.2:
    resolution: {integrity: sha512-mlN83YSrcFgk7Dm1Mys40DLssI1KdJji2CMKN8eOlBqsTADYzj2+jWzsANsUTFbxDMWPD5e9bfA1RGqBpS3O1g==}
    engines: {node: '>=14'}
    dependencies:
      '@types/set-cookie-parser': 2.4.2
      set-cookie-parser: 2.5.1
    dev: true

  /@mswjs/interceptors@0.17.6:
    resolution: {integrity: sha512-201pBIWehTURb6q8Gheu4Zhvd3Ox1U4BJq5KiOQsYzkWyfiOG4pwcz5hPZIEryztgrf8/sdwABpvY757xMmfrQ==}
    engines: {node: '>=14'}
    dependencies:
      '@open-draft/until': 1.0.3
      '@types/debug': 4.1.7
      '@xmldom/xmldom': 0.8.3
      debug: 4.3.4
      headers-polyfill: 3.1.2
      outvariant: 1.3.0
      strict-event-emitter: 0.2.8
      web-encoding: 1.1.5
    transitivePeerDependencies:
      - supports-color
    dev: true

  /@nodelib/fs.scandir@2.1.5:
    resolution: {integrity: sha512-vq24Bq3ym5HEQm2NKCr3yXDwjc7vTsEThRDnkp2DK9p1uqLR+DHurm/NOTo0KG7HYHU7eppKZj3MyqYuMBf62g==}
    engines: {node: '>= 8'}
    dependencies:
      '@nodelib/fs.stat': 2.0.5
      run-parallel: 1.2.0
    dev: true

  /@nodelib/fs.stat@2.0.5:
    resolution: {integrity: sha512-RkhPPp2zrqDAQA/2jNhnztcPAlv64XdhIp7a7454A5ovI7Bukxgt7MX7udwAu3zg1DcpPU0rz3VV1SeaqvY4+A==}
    engines: {node: '>= 8'}
    dev: true

  /@nodelib/fs.walk@1.2.8:
    resolution: {integrity: sha512-oGB+UxlgWcgQkgwo8GcEGwemoTFt3FIO9ababBmaGwXIoBKZ+GTy0pP185beGg7Llih/NSHSV2XAs1lnznocSg==}
    engines: {node: '>= 8'}
    dependencies:
      '@nodelib/fs.scandir': 2.1.5
      fastq: 1.13.0
    dev: true

  /@open-draft/until@1.0.3:
    resolution: {integrity: sha512-Aq58f5HiWdyDlFffbbSjAlv596h/cOnt2DO1w3DOC7OJ5EHs0hd/nycJfiu9RJbT6Yk6F1knnRRXNSpxoIVZ9Q==}
    dev: true

  /@radix-ui/number@1.0.0:
    resolution: {integrity: sha512-Ofwh/1HX69ZfJRiRBMTy7rgjAzHmwe4kW9C9Y99HTRUcYLUuVT0KESFj15rPjRgKJs20GPq8Bm5aEDJ8DuA3vA==}
    dependencies:
      '@babel/runtime': 7.20.7
    dev: false

  /@radix-ui/primitive@1.0.0:
    resolution: {integrity: sha512-3e7rn8FDMin4CgeL7Z/49smCA3rFYY3Ha2rUQ7HRWFadS5iCRw08ZgVT1LaNTCNqgvrUiyczLflrVrF0SRQtNA==}
    dependencies:
      '@babel/runtime': 7.20.7
    dev: false

  /@radix-ui/react-alert-dialog@1.0.3(@types/react@18.0.28)(react-dom@18.2.0)(react@18.2.0):
    resolution: {integrity: sha512-QXFy7+bhGi0u+paF2QbJeSCHZs4gLMJIPm6sajUamyW0fro6g1CaSGc5zmc4QmK2NlSGUrq8m+UsUqJYtzvXow==}
    peerDependencies:
      react: ^16.8 || ^17.0 || ^18.0
      react-dom: ^16.8 || ^17.0 || ^18.0
    dependencies:
      '@babel/runtime': 7.20.7
      '@radix-ui/primitive': 1.0.0
      '@radix-ui/react-compose-refs': 1.0.0(react@18.2.0)
      '@radix-ui/react-context': 1.0.0(react@18.2.0)
      '@radix-ui/react-dialog': 1.0.3(@types/react@18.0.28)(react-dom@18.2.0)(react@18.2.0)
      '@radix-ui/react-primitive': 1.0.2(react-dom@18.2.0)(react@18.2.0)
      '@radix-ui/react-slot': 1.0.1(react@18.2.0)
      react: 18.2.0
      react-dom: 18.2.0(react@18.2.0)
    transitivePeerDependencies:
      - '@types/react'
    dev: false

  /@radix-ui/react-arrow@1.0.2(react-dom@18.2.0)(react@18.2.0):
    resolution: {integrity: sha512-fqYwhhI9IarZ0ll2cUSfKuXHlJK0qE4AfnRrPBbRwEH/4mGQn04/QFGomLi8TXWIdv9WJk//KgGm+aDxVIr1wA==}
    peerDependencies:
      react: ^16.8 || ^17.0 || ^18.0
      react-dom: ^16.8 || ^17.0 || ^18.0
    dependencies:
      '@babel/runtime': 7.20.7
      '@radix-ui/react-primitive': 1.0.2(react-dom@18.2.0)(react@18.2.0)
      react: 18.2.0
      react-dom: 18.2.0(react@18.2.0)
    dev: false

  /@radix-ui/react-collapsible@1.0.2(react-dom@18.2.0)(react@18.2.0):
    resolution: {integrity: sha512-QNiDT6Au8jUU0K1WV+HEd4loH7C5CKQjeXxskwqyiyAkyCmW7qlQM5vSSJCIoQC+OVPyhgafSmGudRP8Qm1/gA==}
    peerDependencies:
      react: ^16.8 || ^17.0 || ^18.0
      react-dom: ^16.8 || ^17.0 || ^18.0
    dependencies:
      '@babel/runtime': 7.20.7
      '@radix-ui/primitive': 1.0.0
      '@radix-ui/react-compose-refs': 1.0.0(react@18.2.0)
      '@radix-ui/react-context': 1.0.0(react@18.2.0)
      '@radix-ui/react-id': 1.0.0(react@18.2.0)
      '@radix-ui/react-presence': 1.0.0(react-dom@18.2.0)(react@18.2.0)
      '@radix-ui/react-primitive': 1.0.2(react-dom@18.2.0)(react@18.2.0)
      '@radix-ui/react-use-controllable-state': 1.0.0(react@18.2.0)
      '@radix-ui/react-use-layout-effect': 1.0.0(react@18.2.0)
      react: 18.2.0
      react-dom: 18.2.0(react@18.2.0)
    dev: false

  /@radix-ui/react-collection@1.0.2(react-dom@18.2.0)(react@18.2.0):
    resolution: {integrity: sha512-s8WdQQ6wNXpaxdZ308KSr8fEWGrg4un8i4r/w7fhiS4ElRNjk5rRcl0/C6TANG2LvLOGIxtzo/jAg6Qf73TEBw==}
    peerDependencies:
      react: ^16.8 || ^17.0 || ^18.0
      react-dom: ^16.8 || ^17.0 || ^18.0
    dependencies:
      '@babel/runtime': 7.20.7
      '@radix-ui/react-compose-refs': 1.0.0(react@18.2.0)
      '@radix-ui/react-context': 1.0.0(react@18.2.0)
      '@radix-ui/react-primitive': 1.0.2(react-dom@18.2.0)(react@18.2.0)
      '@radix-ui/react-slot': 1.0.1(react@18.2.0)
      react: 18.2.0
      react-dom: 18.2.0(react@18.2.0)
    dev: false

  /@radix-ui/react-compose-refs@1.0.0(react@18.2.0):
    resolution: {integrity: sha512-0KaSv6sx787/hK3eF53iOkiSLwAGlFMx5lotrqD2pTjB18KbybKoEIgkNZTKC60YECDQTKGTRcDBILwZVqVKvA==}
    peerDependencies:
      react: ^16.8 || ^17.0 || ^18.0
    dependencies:
      '@babel/runtime': 7.20.7
      react: 18.2.0
    dev: false

  /@radix-ui/react-context@1.0.0(react@18.2.0):
    resolution: {integrity: sha512-1pVM9RfOQ+n/N5PJK33kRSKsr1glNxomxONs5c49MliinBY6Yw2Q995qfBUUo0/Mbg05B/sGA0gkgPI7kmSHBg==}
    peerDependencies:
      react: ^16.8 || ^17.0 || ^18.0
    dependencies:
      '@babel/runtime': 7.20.7
      react: 18.2.0
    dev: false

  /@radix-ui/react-dialog@1.0.3(@types/react@18.0.28)(react-dom@18.2.0)(react@18.2.0):
    resolution: {integrity: sha512-owNhq36kNPqC2/a+zJRioPg6HHnTn5B/sh/NjTY8r4W9g1L5VJlrzZIVcBr7R9Mg8iLjVmh6MGgMlfoVf/WO/A==}
    peerDependencies:
      react: ^16.8 || ^17.0 || ^18.0
      react-dom: ^16.8 || ^17.0 || ^18.0
    dependencies:
      '@babel/runtime': 7.20.7
      '@radix-ui/primitive': 1.0.0
      '@radix-ui/react-compose-refs': 1.0.0(react@18.2.0)
      '@radix-ui/react-context': 1.0.0(react@18.2.0)
      '@radix-ui/react-dismissable-layer': 1.0.3(react-dom@18.2.0)(react@18.2.0)
      '@radix-ui/react-focus-guards': 1.0.0(react@18.2.0)
      '@radix-ui/react-focus-scope': 1.0.2(react-dom@18.2.0)(react@18.2.0)
      '@radix-ui/react-id': 1.0.0(react@18.2.0)
      '@radix-ui/react-portal': 1.0.2(react-dom@18.2.0)(react@18.2.0)
      '@radix-ui/react-presence': 1.0.0(react-dom@18.2.0)(react@18.2.0)
      '@radix-ui/react-primitive': 1.0.2(react-dom@18.2.0)(react@18.2.0)
      '@radix-ui/react-slot': 1.0.1(react@18.2.0)
      '@radix-ui/react-use-controllable-state': 1.0.0(react@18.2.0)
      aria-hidden: 1.2.1(@types/react@18.0.28)(react@18.2.0)
      react: 18.2.0
      react-dom: 18.2.0(react@18.2.0)
      react-remove-scroll: 2.5.5(@types/react@18.0.28)(react@18.2.0)
    transitivePeerDependencies:
      - '@types/react'
    dev: false

  /@radix-ui/react-direction@1.0.0(react@18.2.0):
    resolution: {integrity: sha512-2HV05lGUgYcA6xgLQ4BKPDmtL+QbIZYH5fCOTAOOcJ5O0QbWS3i9lKaurLzliYUDhORI2Qr3pyjhJh44lKA3rQ==}
    peerDependencies:
      react: ^16.8 || ^17.0 || ^18.0
    dependencies:
      '@babel/runtime': 7.20.7
      react: 18.2.0
    dev: false

  /@radix-ui/react-dismissable-layer@1.0.3(react-dom@18.2.0)(react@18.2.0):
    resolution: {integrity: sha512-nXZOvFjOuHS1ovumntGV7NNoLaEp9JEvTht3MBjP44NSW5hUKj/8OnfN3+8WmB+CEhN44XaGhpHoSsUIEl5P7Q==}
    peerDependencies:
      react: ^16.8 || ^17.0 || ^18.0
      react-dom: ^16.8 || ^17.0 || ^18.0
    dependencies:
      '@babel/runtime': 7.20.7
      '@radix-ui/primitive': 1.0.0
      '@radix-ui/react-compose-refs': 1.0.0(react@18.2.0)
      '@radix-ui/react-primitive': 1.0.2(react-dom@18.2.0)(react@18.2.0)
      '@radix-ui/react-use-callback-ref': 1.0.0(react@18.2.0)
      '@radix-ui/react-use-escape-keydown': 1.0.2(react@18.2.0)
      react: 18.2.0
      react-dom: 18.2.0(react@18.2.0)
    dev: false

  /@radix-ui/react-focus-guards@1.0.0(react@18.2.0):
    resolution: {integrity: sha512-UagjDk4ijOAnGu4WMUPj9ahi7/zJJqNZ9ZAiGPp7waUWJO0O1aWXi/udPphI0IUjvrhBsZJGSN66dR2dsueLWQ==}
    peerDependencies:
      react: ^16.8 || ^17.0 || ^18.0
    dependencies:
      '@babel/runtime': 7.20.7
      react: 18.2.0
    dev: false

  /@radix-ui/react-focus-scope@1.0.2(react-dom@18.2.0)(react@18.2.0):
    resolution: {integrity: sha512-spwXlNTfeIprt+kaEWE/qYuYT3ZAqJiAGjN/JgdvgVDTu8yc+HuX+WOWXrKliKnLnwck0F6JDkqIERncnih+4A==}
    peerDependencies:
      react: ^16.8 || ^17.0 || ^18.0
      react-dom: ^16.8 || ^17.0 || ^18.0
    dependencies:
      '@babel/runtime': 7.20.7
      '@radix-ui/react-compose-refs': 1.0.0(react@18.2.0)
      '@radix-ui/react-primitive': 1.0.2(react-dom@18.2.0)(react@18.2.0)
      '@radix-ui/react-use-callback-ref': 1.0.0(react@18.2.0)
      react: 18.2.0
      react-dom: 18.2.0(react@18.2.0)
    dev: false

  /@radix-ui/react-id@1.0.0(react@18.2.0):
    resolution: {integrity: sha512-Q6iAB/U7Tq3NTolBBQbHTgclPmGWE3OlktGGqrClPozSw4vkQ1DfQAOtzgRPecKsMdJINE05iaoDUG8tRzCBjw==}
    peerDependencies:
      react: ^16.8 || ^17.0 || ^18.0
    dependencies:
      '@babel/runtime': 7.20.7
      '@radix-ui/react-use-layout-effect': 1.0.0(react@18.2.0)
      react: 18.2.0
    dev: false

  /@radix-ui/react-popper@1.1.1(@types/react@18.0.28)(react-dom@18.2.0)(react@18.2.0):
    resolution: {integrity: sha512-keYDcdMPNMjSC8zTsZ8wezUMiWM9Yj14wtF3s0PTIs9srnEPC9Kt2Gny1T3T81mmSeyDjZxsD9N5WCwNNb712w==}
    peerDependencies:
      react: ^16.8 || ^17.0 || ^18.0
      react-dom: ^16.8 || ^17.0 || ^18.0
    dependencies:
      '@babel/runtime': 7.20.7
      '@floating-ui/react-dom': 0.7.2(@types/react@18.0.28)(react-dom@18.2.0)(react@18.2.0)
      '@radix-ui/react-arrow': 1.0.2(react-dom@18.2.0)(react@18.2.0)
      '@radix-ui/react-compose-refs': 1.0.0(react@18.2.0)
      '@radix-ui/react-context': 1.0.0(react@18.2.0)
      '@radix-ui/react-primitive': 1.0.2(react-dom@18.2.0)(react@18.2.0)
      '@radix-ui/react-use-callback-ref': 1.0.0(react@18.2.0)
      '@radix-ui/react-use-layout-effect': 1.0.0(react@18.2.0)
      '@radix-ui/react-use-rect': 1.0.0(react@18.2.0)
      '@radix-ui/react-use-size': 1.0.0(react@18.2.0)
      '@radix-ui/rect': 1.0.0
      react: 18.2.0
      react-dom: 18.2.0(react@18.2.0)
    transitivePeerDependencies:
      - '@types/react'
    dev: false

  /@radix-ui/react-portal@1.0.2(react-dom@18.2.0)(react@18.2.0):
    resolution: {integrity: sha512-swu32idoCW7KA2VEiUZGBSu9nB6qwGdV6k6HYhUoOo3M1FFpD+VgLzUqtt3mwL1ssz7r2x8MggpLSQach2Xy/Q==}
    peerDependencies:
      react: ^16.8 || ^17.0 || ^18.0
      react-dom: ^16.8 || ^17.0 || ^18.0
    dependencies:
      '@babel/runtime': 7.20.7
      '@radix-ui/react-primitive': 1.0.2(react-dom@18.2.0)(react@18.2.0)
      react: 18.2.0
      react-dom: 18.2.0(react@18.2.0)
    dev: false

  /@radix-ui/react-presence@1.0.0(react-dom@18.2.0)(react@18.2.0):
    resolution: {integrity: sha512-A+6XEvN01NfVWiKu38ybawfHsBjWum42MRPnEuqPsBZ4eV7e/7K321B5VgYMPv3Xx5An6o1/l9ZuDBgmcmWK3w==}
    peerDependencies:
      react: ^16.8 || ^17.0 || ^18.0
      react-dom: ^16.8 || ^17.0 || ^18.0
    dependencies:
      '@babel/runtime': 7.20.7
      '@radix-ui/react-compose-refs': 1.0.0(react@18.2.0)
      '@radix-ui/react-use-layout-effect': 1.0.0(react@18.2.0)
      react: 18.2.0
      react-dom: 18.2.0(react@18.2.0)
    dev: false

  /@radix-ui/react-primitive@1.0.2(react-dom@18.2.0)(react@18.2.0):
    resolution: {integrity: sha512-zY6G5Qq4R8diFPNwtyoLRZBxzu1Z+SXMlfYpChN7Dv8gvmx9X3qhDqiLWvKseKVJMuedFeU/Sa0Sy/Ia+t06Dw==}
    peerDependencies:
      react: ^16.8 || ^17.0 || ^18.0
      react-dom: ^16.8 || ^17.0 || ^18.0
    dependencies:
      '@babel/runtime': 7.20.7
      '@radix-ui/react-slot': 1.0.1(react@18.2.0)
      react: 18.2.0
      react-dom: 18.2.0(react@18.2.0)
    dev: false

  /@radix-ui/react-roving-focus@1.0.3(react-dom@18.2.0)(react@18.2.0):
    resolution: {integrity: sha512-stjCkIoMe6h+1fWtXlA6cRfikdBzCLp3SnVk7c48cv/uy3DTGoXhN76YaOYUJuy3aEDvDIKwKR5KSmvrtPvQPQ==}
    peerDependencies:
      react: ^16.8 || ^17.0 || ^18.0
      react-dom: ^16.8 || ^17.0 || ^18.0
    dependencies:
      '@babel/runtime': 7.20.7
      '@radix-ui/primitive': 1.0.0
      '@radix-ui/react-collection': 1.0.2(react-dom@18.2.0)(react@18.2.0)
      '@radix-ui/react-compose-refs': 1.0.0(react@18.2.0)
      '@radix-ui/react-context': 1.0.0(react@18.2.0)
      '@radix-ui/react-direction': 1.0.0(react@18.2.0)
      '@radix-ui/react-id': 1.0.0(react@18.2.0)
      '@radix-ui/react-primitive': 1.0.2(react-dom@18.2.0)(react@18.2.0)
      '@radix-ui/react-use-callback-ref': 1.0.0(react@18.2.0)
      '@radix-ui/react-use-controllable-state': 1.0.0(react@18.2.0)
      react: 18.2.0
      react-dom: 18.2.0(react@18.2.0)
    dev: false

  /@radix-ui/react-select@1.2.1(@types/react@18.0.28)(react-dom@18.2.0)(react@18.2.0):
    resolution: {integrity: sha512-GULRMITaOHNj79BZvQs3iZO0+f2IgI8g5HDhMi7Bnc13t7IlG86NFtOCfTLme4PNZdEtU+no+oGgcl6IFiphpQ==}
    peerDependencies:
      react: ^16.8 || ^17.0 || ^18.0
      react-dom: ^16.8 || ^17.0 || ^18.0
    dependencies:
      '@babel/runtime': 7.20.7
      '@radix-ui/number': 1.0.0
      '@radix-ui/primitive': 1.0.0
      '@radix-ui/react-collection': 1.0.2(react-dom@18.2.0)(react@18.2.0)
      '@radix-ui/react-compose-refs': 1.0.0(react@18.2.0)
      '@radix-ui/react-context': 1.0.0(react@18.2.0)
      '@radix-ui/react-direction': 1.0.0(react@18.2.0)
      '@radix-ui/react-dismissable-layer': 1.0.3(react-dom@18.2.0)(react@18.2.0)
      '@radix-ui/react-focus-guards': 1.0.0(react@18.2.0)
      '@radix-ui/react-focus-scope': 1.0.2(react-dom@18.2.0)(react@18.2.0)
      '@radix-ui/react-id': 1.0.0(react@18.2.0)
      '@radix-ui/react-popper': 1.1.1(@types/react@18.0.28)(react-dom@18.2.0)(react@18.2.0)
      '@radix-ui/react-portal': 1.0.2(react-dom@18.2.0)(react@18.2.0)
      '@radix-ui/react-primitive': 1.0.2(react-dom@18.2.0)(react@18.2.0)
      '@radix-ui/react-slot': 1.0.1(react@18.2.0)
      '@radix-ui/react-use-callback-ref': 1.0.0(react@18.2.0)
      '@radix-ui/react-use-controllable-state': 1.0.0(react@18.2.0)
      '@radix-ui/react-use-layout-effect': 1.0.0(react@18.2.0)
      '@radix-ui/react-use-previous': 1.0.0(react@18.2.0)
      '@radix-ui/react-visually-hidden': 1.0.2(react-dom@18.2.0)(react@18.2.0)
      aria-hidden: 1.2.1(@types/react@18.0.28)(react@18.2.0)
      react: 18.2.0
      react-dom: 18.2.0(react@18.2.0)
      react-remove-scroll: 2.5.5(@types/react@18.0.28)(react@18.2.0)
    transitivePeerDependencies:
      - '@types/react'
    dev: false

  /@radix-ui/react-slider@1.1.1(react-dom@18.2.0)(react@18.2.0):
    resolution: {integrity: sha512-0aswLpUKZIraPEOcXfwW25N1KPfLA6Mvm1TxogUChGsbLbys2ihd7uk9XAKsol9ZQPucxh2/mybwdRtAKrs/MQ==}
    peerDependencies:
      react: ^16.8 || ^17.0 || ^18.0
      react-dom: ^16.8 || ^17.0 || ^18.0
    dependencies:
      '@babel/runtime': 7.20.7
      '@radix-ui/number': 1.0.0
      '@radix-ui/primitive': 1.0.0
      '@radix-ui/react-collection': 1.0.2(react-dom@18.2.0)(react@18.2.0)
      '@radix-ui/react-compose-refs': 1.0.0(react@18.2.0)
      '@radix-ui/react-context': 1.0.0(react@18.2.0)
      '@radix-ui/react-direction': 1.0.0(react@18.2.0)
      '@radix-ui/react-primitive': 1.0.2(react-dom@18.2.0)(react@18.2.0)
      '@radix-ui/react-use-controllable-state': 1.0.0(react@18.2.0)
      '@radix-ui/react-use-layout-effect': 1.0.0(react@18.2.0)
      '@radix-ui/react-use-previous': 1.0.0(react@18.2.0)
      '@radix-ui/react-use-size': 1.0.0(react@18.2.0)
      react: 18.2.0
      react-dom: 18.2.0(react@18.2.0)
    dev: false

  /@radix-ui/react-slot@1.0.1(react@18.2.0):
    resolution: {integrity: sha512-avutXAFL1ehGvAXtPquu0YK5oz6ctS474iM3vNGQIkswrVhdrS52e3uoMQBzZhNRAIE0jBnUyXWNmSjGHhCFcw==}
    peerDependencies:
      react: ^16.8 || ^17.0 || ^18.0
    dependencies:
      '@babel/runtime': 7.20.7
      '@radix-ui/react-compose-refs': 1.0.0(react@18.2.0)
      react: 18.2.0
    dev: false

  /@radix-ui/react-switch@1.0.2(react-dom@18.2.0)(react@18.2.0):
    resolution: {integrity: sha512-BcG/LKehxt36NXG0wPnoCitIfSMtU9Xo7BmythYA1PAMLtsMvW7kALfBzmduQoHTWcKr0AVcFyh0gChBUp9TiQ==}
    peerDependencies:
      react: ^16.8 || ^17.0 || ^18.0
      react-dom: ^16.8 || ^17.0 || ^18.0
    dependencies:
      '@babel/runtime': 7.20.7
      '@radix-ui/primitive': 1.0.0
      '@radix-ui/react-compose-refs': 1.0.0(react@18.2.0)
      '@radix-ui/react-context': 1.0.0(react@18.2.0)
      '@radix-ui/react-primitive': 1.0.2(react-dom@18.2.0)(react@18.2.0)
      '@radix-ui/react-use-controllable-state': 1.0.0(react@18.2.0)
      '@radix-ui/react-use-previous': 1.0.0(react@18.2.0)
      '@radix-ui/react-use-size': 1.0.0(react@18.2.0)
      react: 18.2.0
      react-dom: 18.2.0(react@18.2.0)
    dev: false

  /@radix-ui/react-toast@1.1.3(react-dom@18.2.0)(react@18.2.0):
    resolution: {integrity: sha512-yHFgpxi9wjbfPvpSPdYAzivCqw48eA1ofT8m/WqYOVTxKPdmQMuVKRYPlMmj4C1d6tJdFj/LBa1J4iY3fL4OwQ==}
    peerDependencies:
      react: ^16.8 || ^17.0 || ^18.0
      react-dom: ^16.8 || ^17.0 || ^18.0
    dependencies:
      '@babel/runtime': 7.20.7
      '@radix-ui/primitive': 1.0.0
      '@radix-ui/react-collection': 1.0.2(react-dom@18.2.0)(react@18.2.0)
      '@radix-ui/react-compose-refs': 1.0.0(react@18.2.0)
      '@radix-ui/react-context': 1.0.0(react@18.2.0)
      '@radix-ui/react-dismissable-layer': 1.0.3(react-dom@18.2.0)(react@18.2.0)
      '@radix-ui/react-portal': 1.0.2(react-dom@18.2.0)(react@18.2.0)
      '@radix-ui/react-presence': 1.0.0(react-dom@18.2.0)(react@18.2.0)
      '@radix-ui/react-primitive': 1.0.2(react-dom@18.2.0)(react@18.2.0)
      '@radix-ui/react-use-callback-ref': 1.0.0(react@18.2.0)
      '@radix-ui/react-use-controllable-state': 1.0.0(react@18.2.0)
      '@radix-ui/react-use-layout-effect': 1.0.0(react@18.2.0)
      '@radix-ui/react-visually-hidden': 1.0.2(react-dom@18.2.0)(react@18.2.0)
      react: 18.2.0
      react-dom: 18.2.0(react@18.2.0)
    dev: false

  /@radix-ui/react-toggle-group@1.0.3(react-dom@18.2.0)(react@18.2.0):
    resolution: {integrity: sha512-fl7yQ3Ty9+jeWb+TwzMkidXhTgFc5HKFxaEDn9nShjLPS1ya/bA5t2JK8wkUaUH6mo6yU+M3vcmUkxnchlXYtw==}
    peerDependencies:
      react: ^16.8 || ^17.0 || ^18.0
      react-dom: ^16.8 || ^17.0 || ^18.0
    dependencies:
      '@babel/runtime': 7.20.7
      '@radix-ui/primitive': 1.0.0
      '@radix-ui/react-context': 1.0.0(react@18.2.0)
      '@radix-ui/react-direction': 1.0.0(react@18.2.0)
      '@radix-ui/react-primitive': 1.0.2(react-dom@18.2.0)(react@18.2.0)
      '@radix-ui/react-roving-focus': 1.0.3(react-dom@18.2.0)(react@18.2.0)
      '@radix-ui/react-toggle': 1.0.2(react-dom@18.2.0)(react@18.2.0)
      '@radix-ui/react-use-controllable-state': 1.0.0(react@18.2.0)
      react: 18.2.0
      react-dom: 18.2.0(react@18.2.0)
    dev: false

  /@radix-ui/react-toggle@1.0.2(react-dom@18.2.0)(react@18.2.0):
    resolution: {integrity: sha512-1MhVrHjgdmYDBgBpmOB0sjK096gFrVqUocsHNapkOTkZIxOwjpGxnW9e24CjQQX9D/c57dI6E8zAAdeAeIdY8g==}
    peerDependencies:
      react: ^16.8 || ^17.0 || ^18.0
      react-dom: ^16.8 || ^17.0 || ^18.0
    dependencies:
      '@babel/runtime': 7.20.7
      '@radix-ui/primitive': 1.0.0
      '@radix-ui/react-primitive': 1.0.2(react-dom@18.2.0)(react@18.2.0)
      '@radix-ui/react-use-controllable-state': 1.0.0(react@18.2.0)
      react: 18.2.0
      react-dom: 18.2.0(react@18.2.0)
    dev: false

  /@radix-ui/react-use-callback-ref@1.0.0(react@18.2.0):
    resolution: {integrity: sha512-GZtyzoHz95Rhs6S63D2t/eqvdFCm7I+yHMLVQheKM7nBD8mbZIt+ct1jz4536MDnaOGKIxynJ8eHTkVGVVkoTg==}
    peerDependencies:
      react: ^16.8 || ^17.0 || ^18.0
    dependencies:
      '@babel/runtime': 7.20.7
      react: 18.2.0
    dev: false

  /@radix-ui/react-use-controllable-state@1.0.0(react@18.2.0):
    resolution: {integrity: sha512-FohDoZvk3mEXh9AWAVyRTYR4Sq7/gavuofglmiXB2g1aKyboUD4YtgWxKj8O5n+Uak52gXQ4wKz5IFST4vtJHg==}
    peerDependencies:
      react: ^16.8 || ^17.0 || ^18.0
    dependencies:
      '@babel/runtime': 7.20.7
      '@radix-ui/react-use-callback-ref': 1.0.0(react@18.2.0)
      react: 18.2.0
    dev: false

  /@radix-ui/react-use-escape-keydown@1.0.2(react@18.2.0):
    resolution: {integrity: sha512-DXGim3x74WgUv+iMNCF+cAo8xUHHeqvjx8zs7trKf+FkQKPQXLk2sX7Gx1ysH7Q76xCpZuxIJE7HLPxRE+Q+GA==}
    peerDependencies:
      react: ^16.8 || ^17.0 || ^18.0
    dependencies:
      '@babel/runtime': 7.20.7
      '@radix-ui/react-use-callback-ref': 1.0.0(react@18.2.0)
      react: 18.2.0
    dev: false

  /@radix-ui/react-use-layout-effect@1.0.0(react@18.2.0):
    resolution: {integrity: sha512-6Tpkq+R6LOlmQb1R5NNETLG0B4YP0wc+klfXafpUCj6JGyaUc8il7/kUZ7m59rGbXGczE9Bs+iz2qloqsZBduQ==}
    peerDependencies:
      react: ^16.8 || ^17.0 || ^18.0
    dependencies:
      '@babel/runtime': 7.20.7
      react: 18.2.0
    dev: false

  /@radix-ui/react-use-previous@1.0.0(react@18.2.0):
    resolution: {integrity: sha512-RG2K8z/K7InnOKpq6YLDmT49HGjNmrK+fr82UCVKT2sW0GYfVnYp4wZWBooT/EYfQ5faA9uIjvsuMMhH61rheg==}
    peerDependencies:
      react: ^16.8 || ^17.0 || ^18.0
    dependencies:
      '@babel/runtime': 7.20.7
      react: 18.2.0
    dev: false

  /@radix-ui/react-use-rect@1.0.0(react@18.2.0):
    resolution: {integrity: sha512-TB7pID8NRMEHxb/qQJpvSt3hQU4sqNPM1VCTjTRjEOa7cEop/QMuq8S6fb/5Tsz64kqSvB9WnwsDHtjnrM9qew==}
    peerDependencies:
      react: ^16.8 || ^17.0 || ^18.0
    dependencies:
      '@babel/runtime': 7.20.7
      '@radix-ui/rect': 1.0.0
      react: 18.2.0
    dev: false

  /@radix-ui/react-use-size@1.0.0(react@18.2.0):
    resolution: {integrity: sha512-imZ3aYcoYCKhhgNpkNDh/aTiU05qw9hX+HHI1QDBTyIlcFjgeFlKKySNGMwTp7nYFLQg/j0VA2FmCY4WPDDHMg==}
    peerDependencies:
      react: ^16.8 || ^17.0 || ^18.0
    dependencies:
      '@babel/runtime': 7.20.7
      '@radix-ui/react-use-layout-effect': 1.0.0(react@18.2.0)
      react: 18.2.0
    dev: false

  /@radix-ui/react-visually-hidden@1.0.2(react-dom@18.2.0)(react@18.2.0):
    resolution: {integrity: sha512-qirnJxtYn73HEk1rXL12/mXnu2rwsNHDID10th2JGtdK25T9wX+mxRmGt7iPSahw512GbZOc0syZX1nLQGoEOg==}
    peerDependencies:
      react: ^16.8 || ^17.0 || ^18.0
      react-dom: ^16.8 || ^17.0 || ^18.0
    dependencies:
      '@babel/runtime': 7.20.7
      '@radix-ui/react-primitive': 1.0.2(react-dom@18.2.0)(react@18.2.0)
      react: 18.2.0
      react-dom: 18.2.0(react@18.2.0)
    dev: false

  /@radix-ui/rect@1.0.0:
    resolution: {integrity: sha512-d0O68AYy/9oeEy1DdC07bz1/ZXX+DqCskRd3i4JzLSTXwefzaepQrKjXC7aNM8lTHjFLDO0pDgaEiQ7jEk+HVg==}
    dependencies:
      '@babel/runtime': 7.20.7
    dev: false

  /@rollup/pluginutils@5.0.2:
    resolution: {integrity: sha512-pTd9rIsP92h+B6wWwFbW8RkZv4hiR/xKsqre4SIuAOaOEQRxi0lqLke9k2/7WegC85GgUs9pjmOjCUi3In4vwA==}
    engines: {node: '>=14.0.0'}
    peerDependencies:
      rollup: ^1.20.0||^2.0.0||^3.0.0
    peerDependenciesMeta:
      rollup:
        optional: true
    dependencies:
      '@types/estree': 1.0.0
      estree-walker: 2.0.2
      picomatch: 2.3.1
    dev: true

  /@svgr/babel-plugin-add-jsx-attribute@6.5.1(@babel/core@7.20.5):
    resolution: {integrity: sha512-9PYGcXrAxitycIjRmZB+Q0JaN07GZIWaTBIGQzfaZv+qr1n8X1XUEJ5rZ/vx6OVD9RRYlrNnXWExQXcmZeD/BQ==}
    engines: {node: '>=10'}
    peerDependencies:
      '@babel/core': ^7.0.0-0
    dependencies:
      '@babel/core': 7.20.5
    dev: true

  /@svgr/babel-plugin-remove-jsx-attribute@6.5.0(@babel/core@7.20.5):
    resolution: {integrity: sha512-8zYdkym7qNyfXpWvu4yq46k41pyNM9SOstoWhKlm+IfdCE1DdnRKeMUPsWIEO/DEkaWxJ8T9esNdG3QwQ93jBA==}
    engines: {node: '>=10'}
    peerDependencies:
      '@babel/core': ^7.0.0-0
    dependencies:
      '@babel/core': 7.20.5
    dev: true

  /@svgr/babel-plugin-remove-jsx-empty-expression@6.5.0(@babel/core@7.20.5):
    resolution: {integrity: sha512-NFdxMq3xA42Kb1UbzCVxplUc0iqSyM9X8kopImvFnB+uSDdzIHOdbs1op8ofAvVRtbg4oZiyRl3fTYeKcOe9Iw==}
    engines: {node: '>=10'}
    peerDependencies:
      '@babel/core': ^7.0.0-0
    dependencies:
      '@babel/core': 7.20.5
    dev: true

  /@svgr/babel-plugin-replace-jsx-attribute-value@6.5.1(@babel/core@7.20.5):
    resolution: {integrity: sha512-8DPaVVE3fd5JKuIC29dqyMB54sA6mfgki2H2+swh+zNJoynC8pMPzOkidqHOSc6Wj032fhl8Z0TVn1GiPpAiJg==}
    engines: {node: '>=10'}
    peerDependencies:
      '@babel/core': ^7.0.0-0
    dependencies:
      '@babel/core': 7.20.5
    dev: true
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
